jimmys01/rfm69gw/images/20160819_002242.jpg

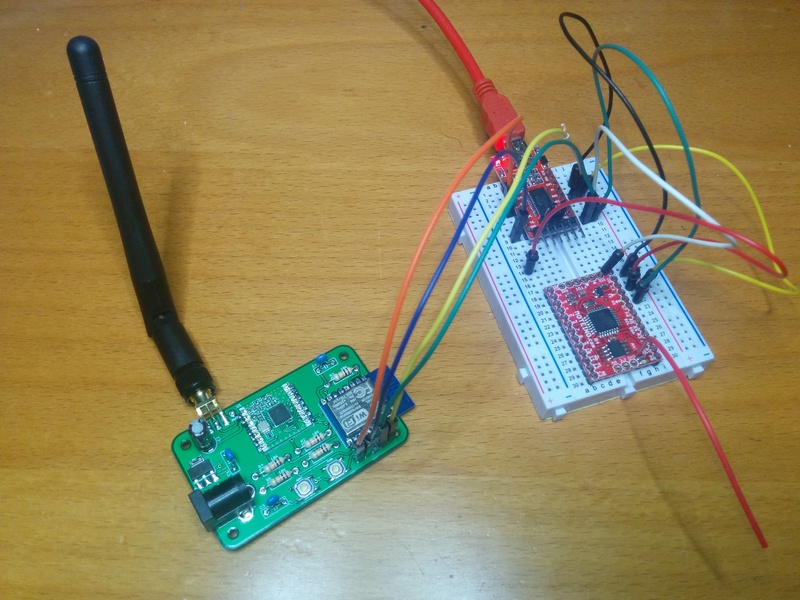
images/20160819_002242.jpg
