jimmys01/rfm69gw/schema/rfm69gw-0.3.20160731-bottom.png

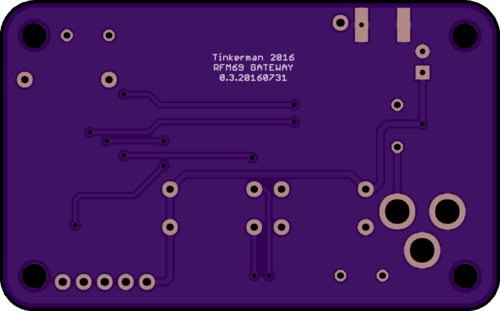
schema/rfm69gw-0.3.20160731-bottom.png
